taylorzr/goshawk/img/20240203_150712.jpg

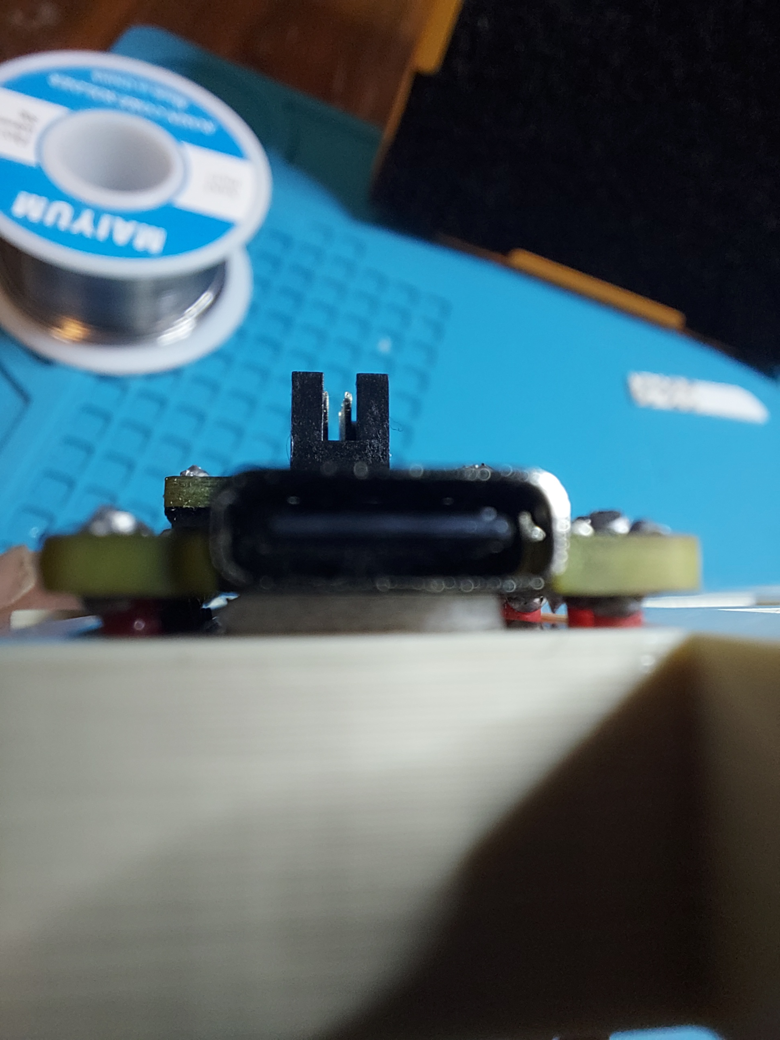
img/20240203_150712.jpg
